SeymurD/homemade-cybertruck/Cybertruck Models/models/Chassis Parts/90_deg_dual_side_mount_d.STEP

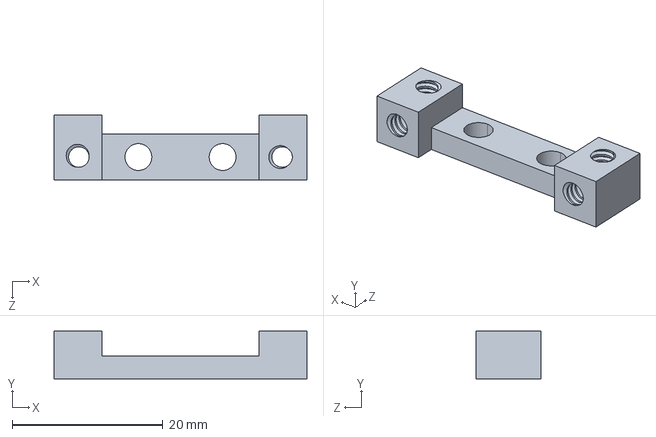
[picture p22: CAD file, 2020-12-03]
Cybertruck Models/models/Chassis Parts/90_deg_dual_side_mount_d.STEP
33.5 x 6.34 x 8.63 mm
