SeymurD/homemade-cybertruck/Cybertruck Models/models/Exterior Design/files/AT_tyre_right.stl

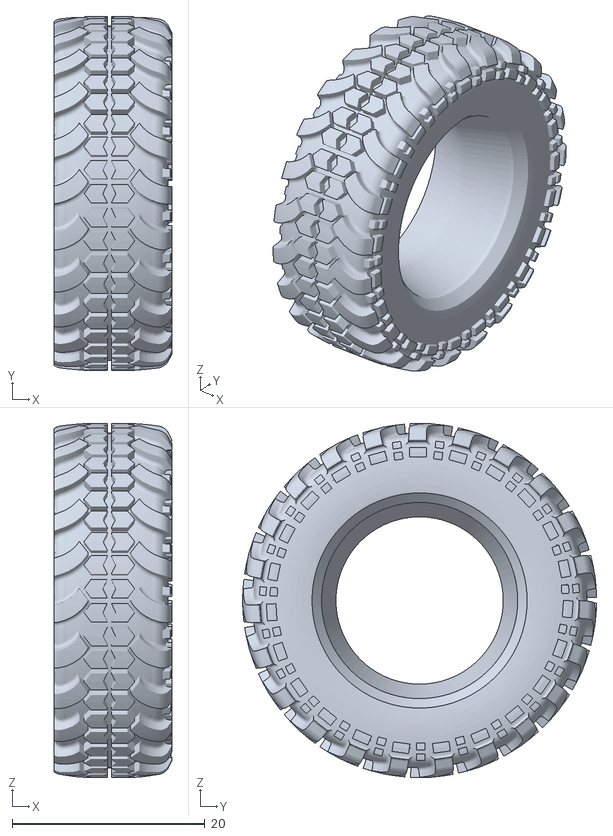
[picture p23: CAD file, 2020-12-03]
Cybertruck Models/models/Exterior Design/files/AT_tyre_right.stl
12.2 x 36.8 x 36.7
