SeymurD/homemade-cybertruck/Cybertruck Models/models/Chassis Parts/hole_aluminum_beams.STEP

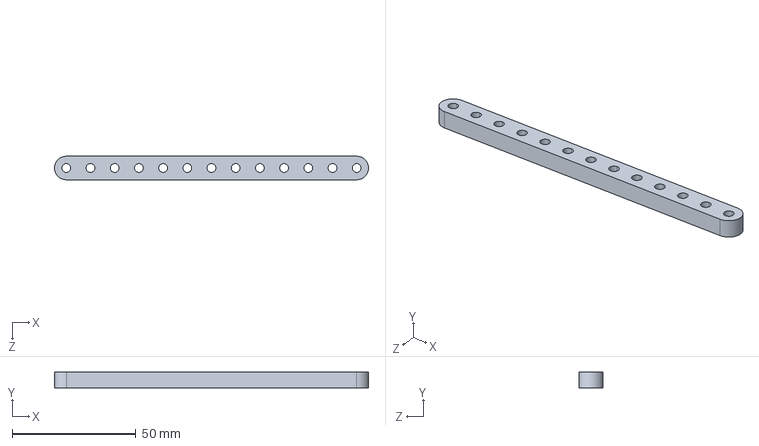
[picture p24: CAD file, 2020-12-03]
Cybertruck Models/models/Chassis Parts/hole_aluminum_beams.STEP
126.9 x 6.35 x 9.53 mm
