SeymurD/homemade-cybertruck/Cybertruck Models/models/Exterior Design/files/black_windscreen.stl

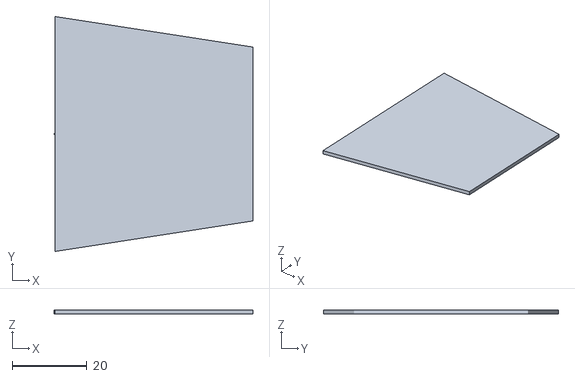
[picture p25: CAD file, 2020-12-03]
Cybertruck Models/models/Exterior Design/files/black_windscreen.stl
53.1 x 62.7 x 1.20
