SeymurD/homemade-cybertruck/Cybertruck Models/models/Chassis Parts/standoff_1-4.STEP

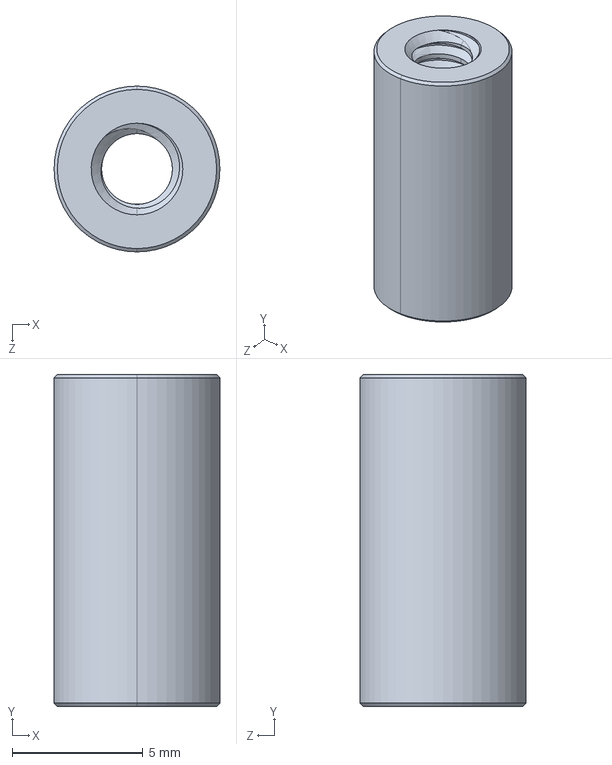
[picture p26: CAD file, 2020-12-03]
Cybertruck Models/models/Chassis Parts/standoff_1-4.STEP
6.34 x 12.7 x 6.34 mm
