SeymurD/homemade-cybertruck/Cybertruck Models/models/Exterior Design/files/black_rim_inside.stl

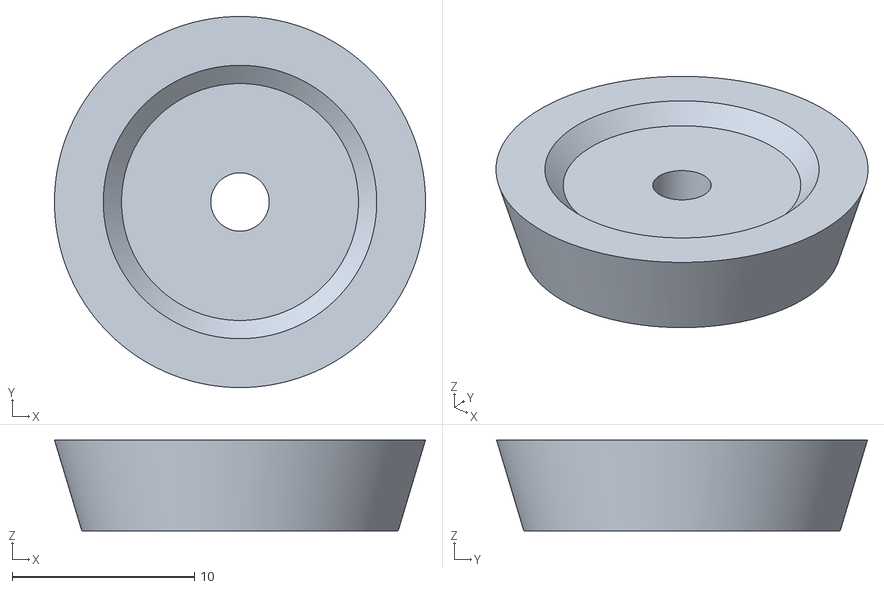
[picture p27: CAD file, 2020-12-03]
Cybertruck Models/models/Exterior Design/files/black_rim_inside.stl
20.4 x 20.4 x 4.99
