SeymurD/homemade-cybertruck/Cybertruck Models/models/Chassis Parts/DC Planeary Gear Motor v1.step

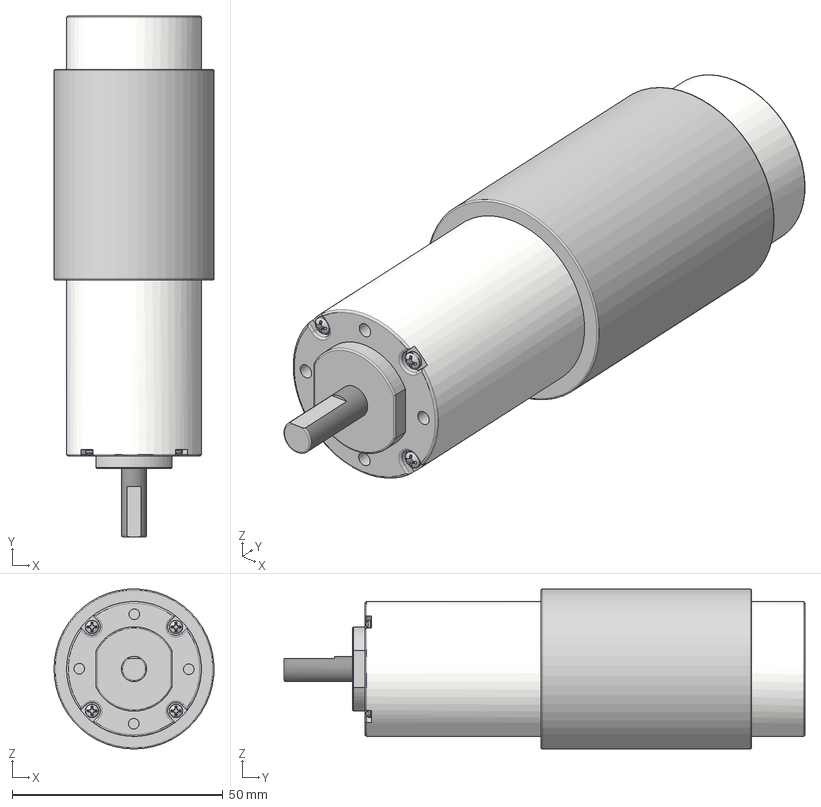
[picture p28: CAD file, 2020-12-03]
Cybertruck Models/models/Chassis Parts/DC Planeary Gear Motor v1.step
38.0 x 123.6 x 38.0 mm
92000A005 x 4
motor drive shaft
motor body
