SeymurD/homemade-cybertruck/Cybertruck Models/models/Exterior Design/files/black_window_left.stl

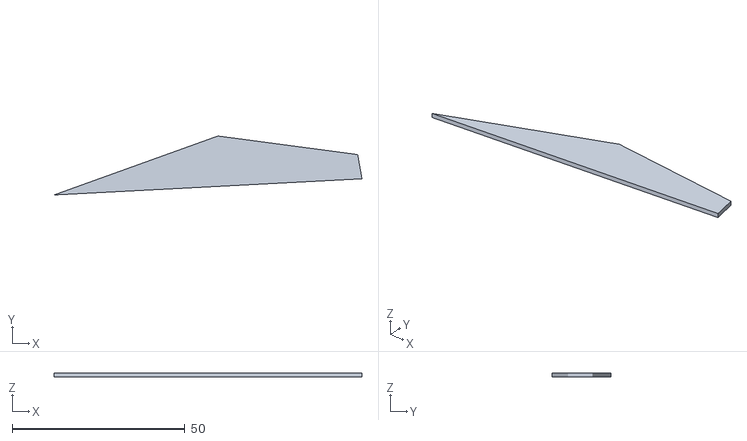
[picture p29: CAD file, 2020-12-03]
Cybertruck Models/models/Exterior Design/files/black_window_left.stl
89.2 x 17.1 x 1.20
