SeymurD/homemade-cybertruck/Cybertruck Models/models/Exterior Design/files/black_rim_outside.stl

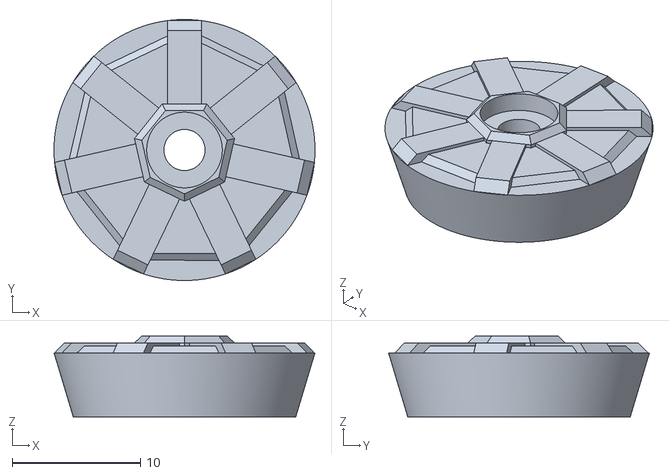
[picture p30: CAD file, 2020-12-03]
Cybertruck Models/models/Exterior Design/files/black_rim_outside.stl
20.4 x 20.4 x 6.30
